richardhawthorn/3x7Segment/images/19-DSC_3821.JPG

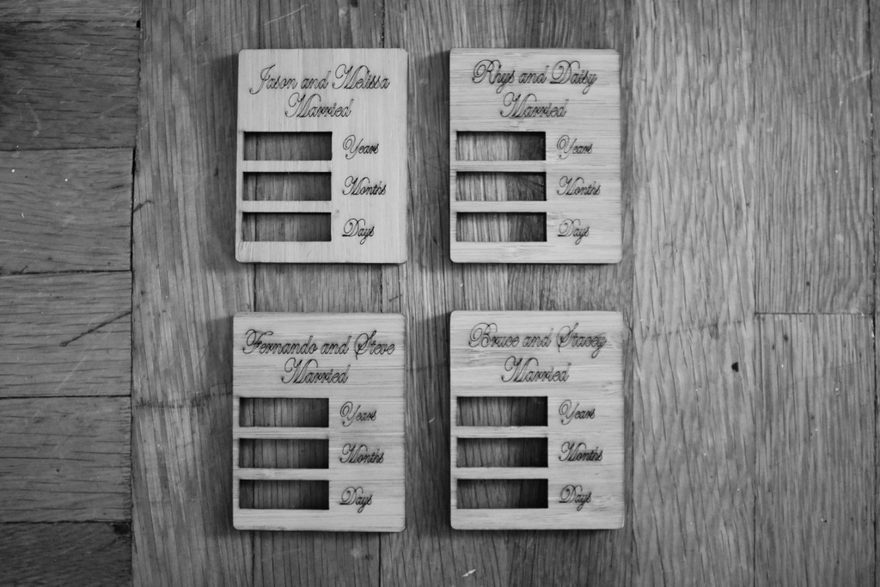
images/19-DSC_3821.JPG
