richardhawthorn/3x7Segment/images/20-DSC_3878.JPG

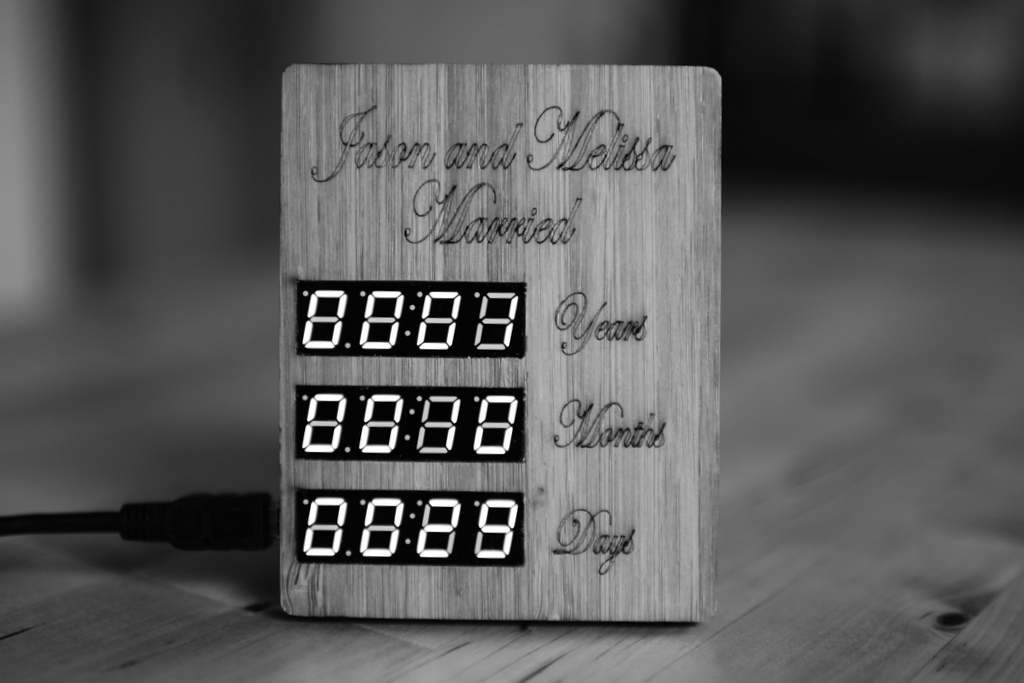
images/20-DSC_3878.JPG
