richardhawthorn/3x7Segment/images/pcb_back_v2_black.png

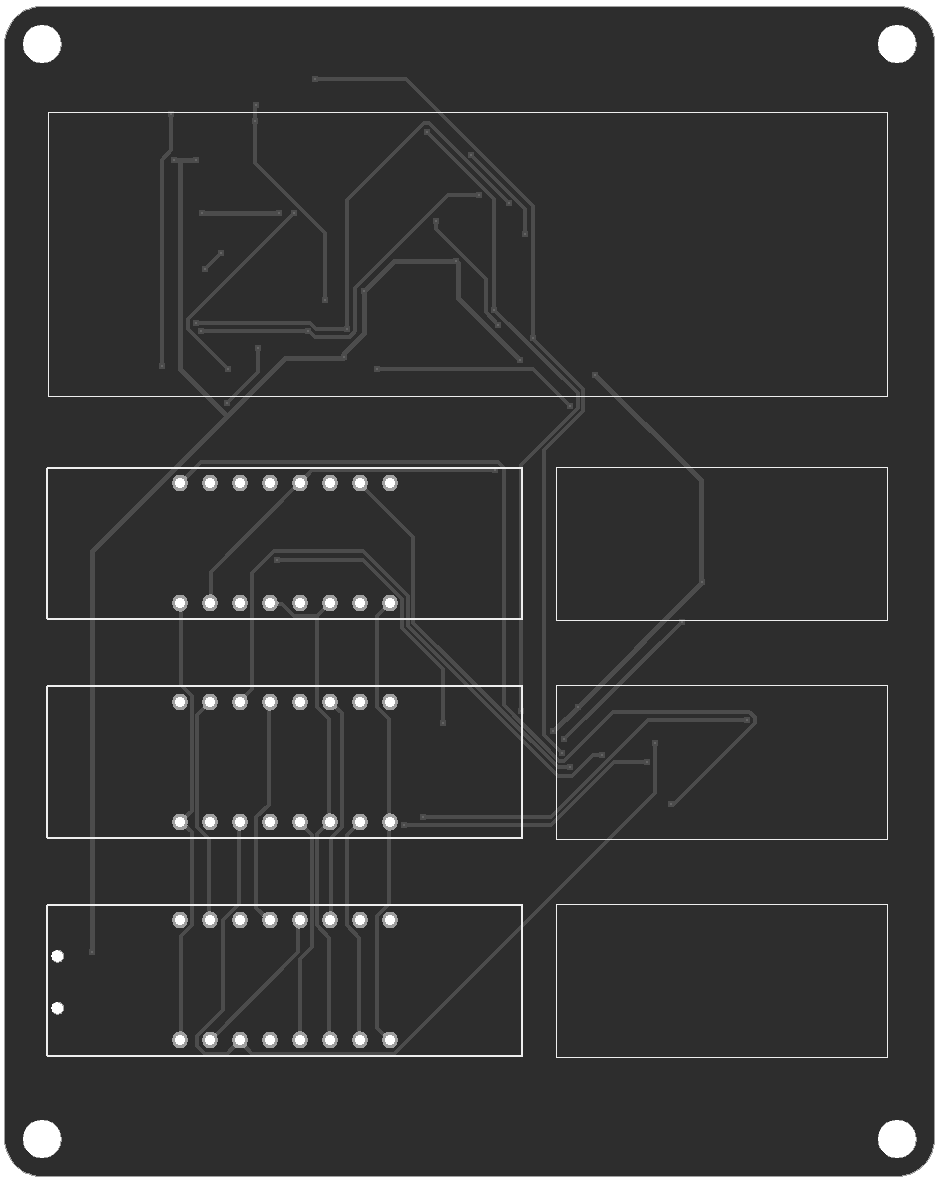
images/pcb_back_v2_black.png
