richardhawthorn/3x7Segment/images/pcb_front_v2.png

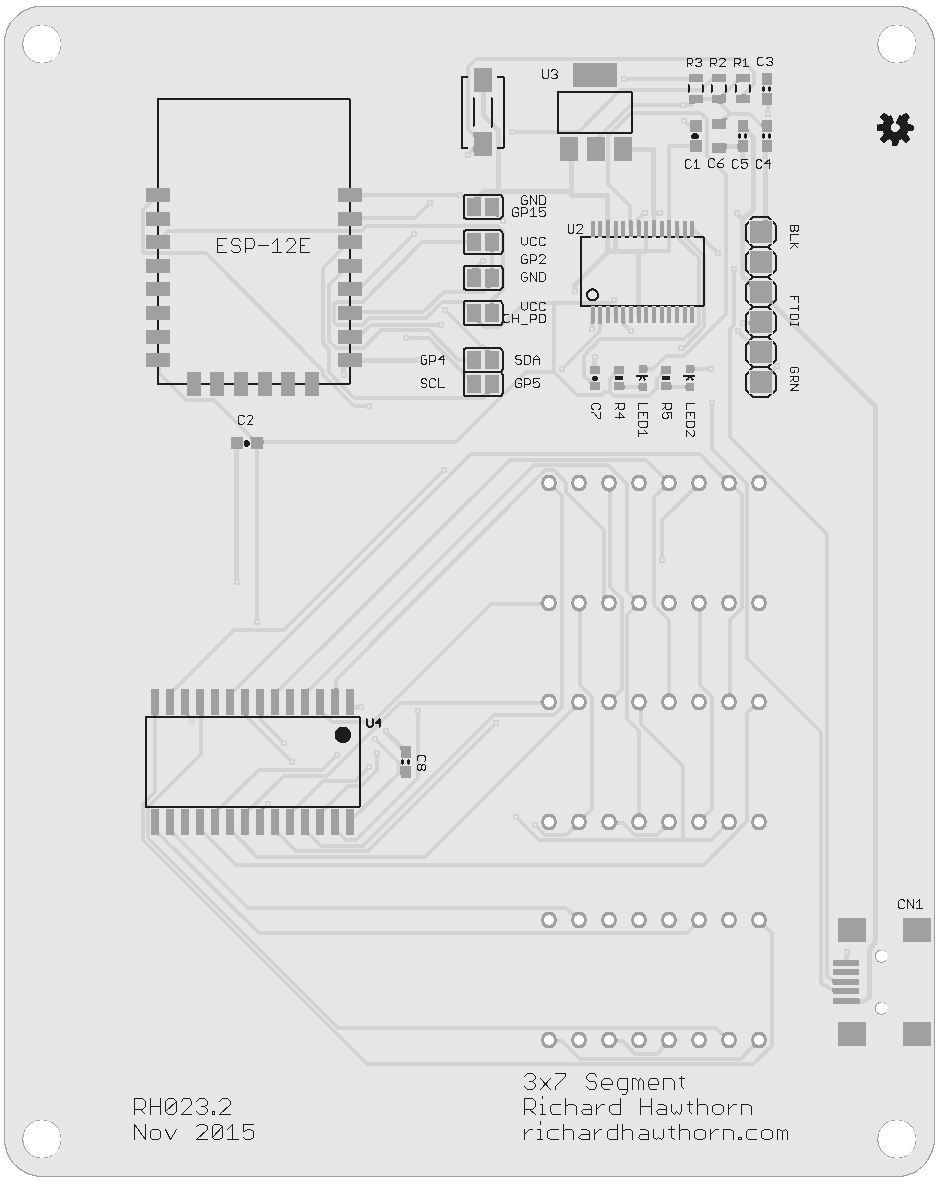
images/pcb_front_v2.png
